kdcgarber/TRS-IO-SSD1306-M1/doc/rsc.png

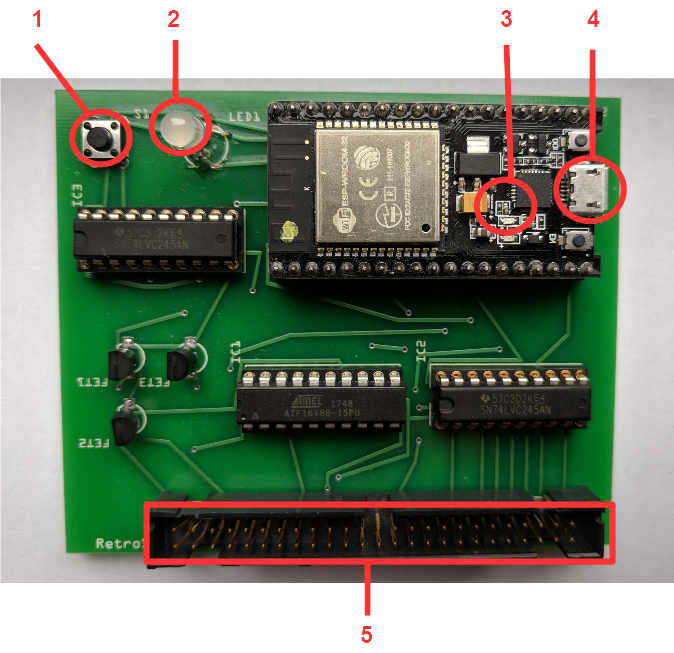
doc/rsc.png
