kdcgarber/TRS-IO-SSD1306-M1/doc/rsclient-1.png

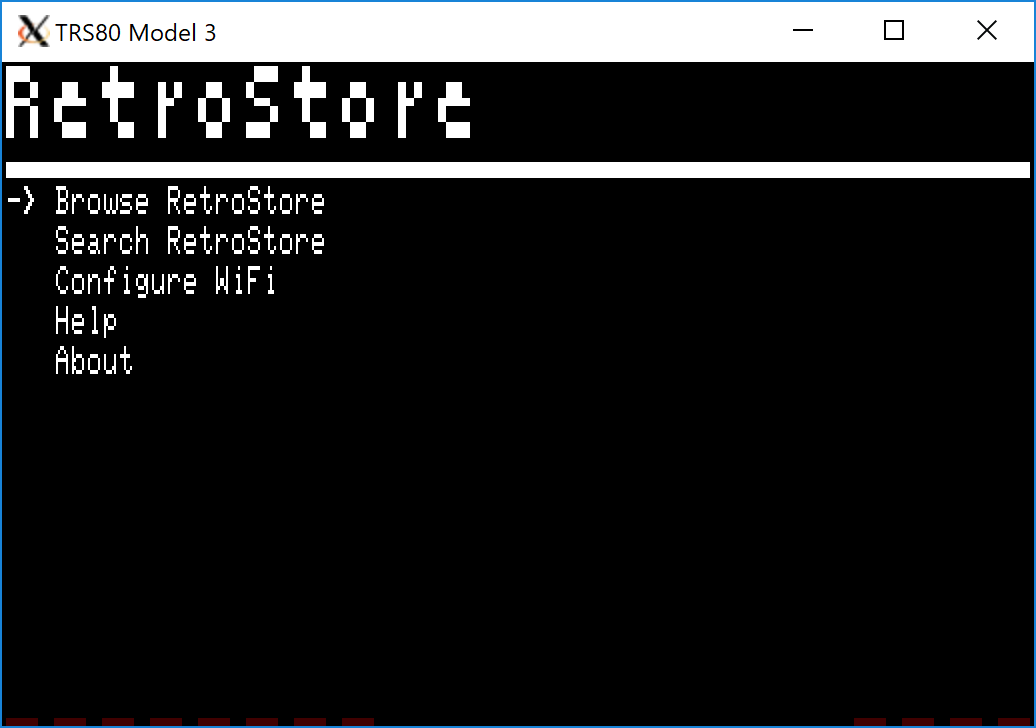
doc/rsclient-1.png
