kdcgarber/TRS-IO-SSD1306-M1/doc/trs-io-architecture.png

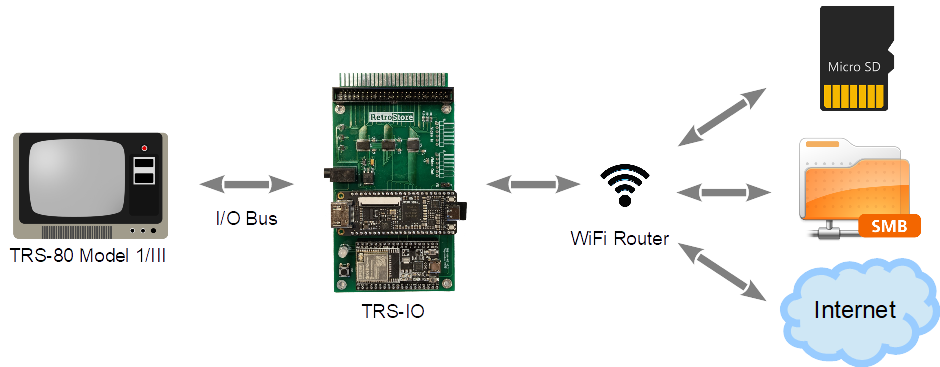
doc/trs-io-architecture.png
