kdcgarber/TRS-IO-SSD1306-M1/doc/trs-io-card-v1-labels.png

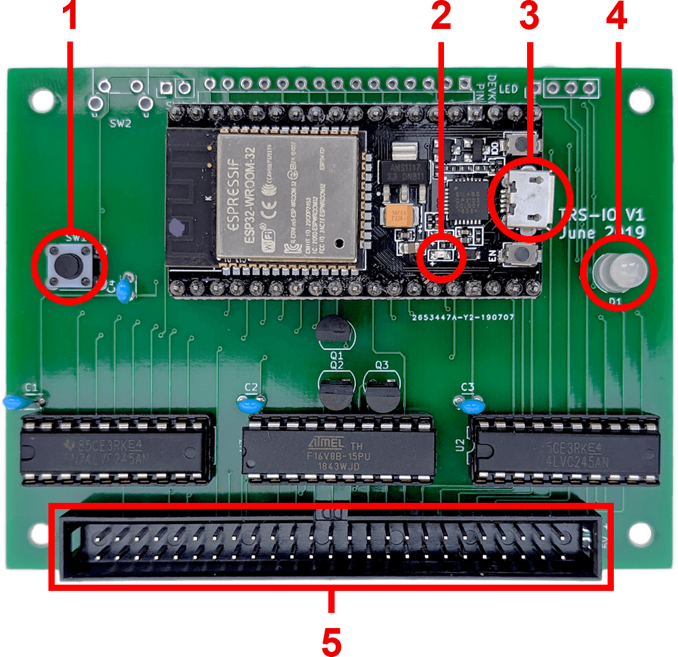
doc/trs-io-card-v1-labels.png
