kdcgarber/TRS-IO-SSD1306-M1/doc/trs-io-card-v1.png

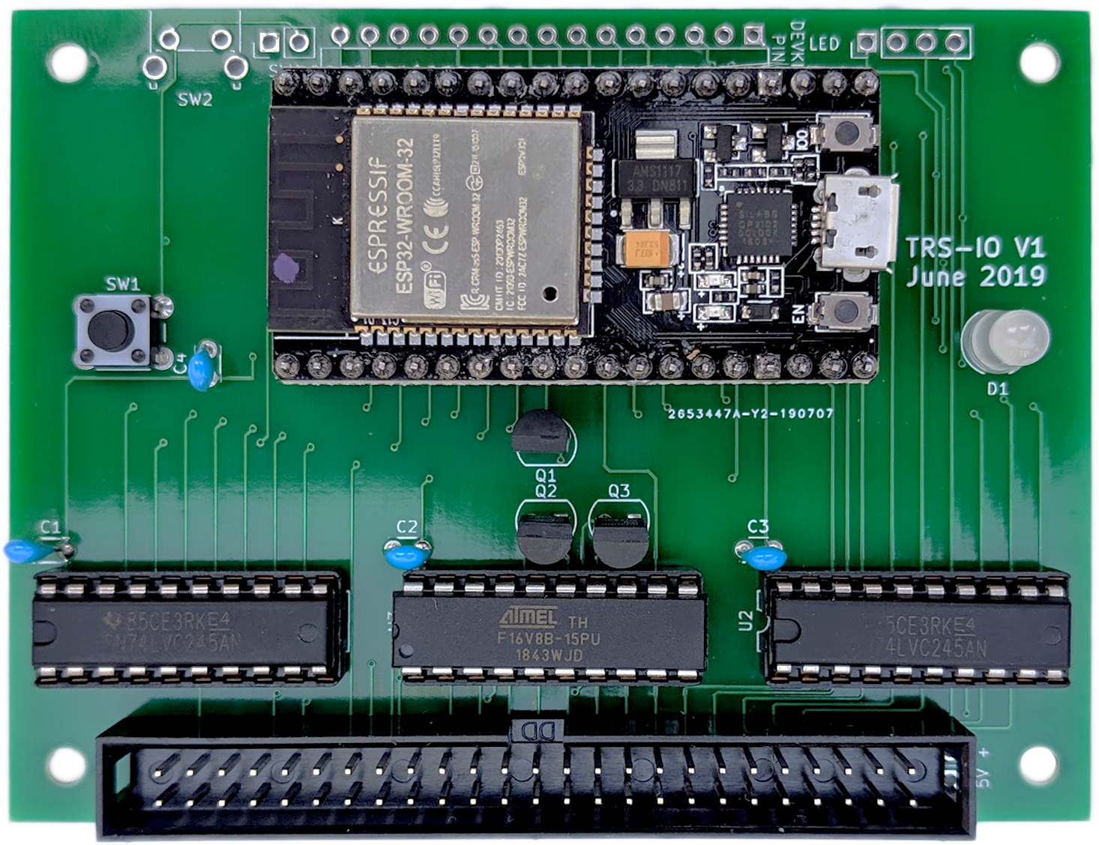
doc/trs-io-card-v1.png
