kdcgarber/TRS-IO-SSD1306-M1/doc/TRS-IO-M1-labels.png

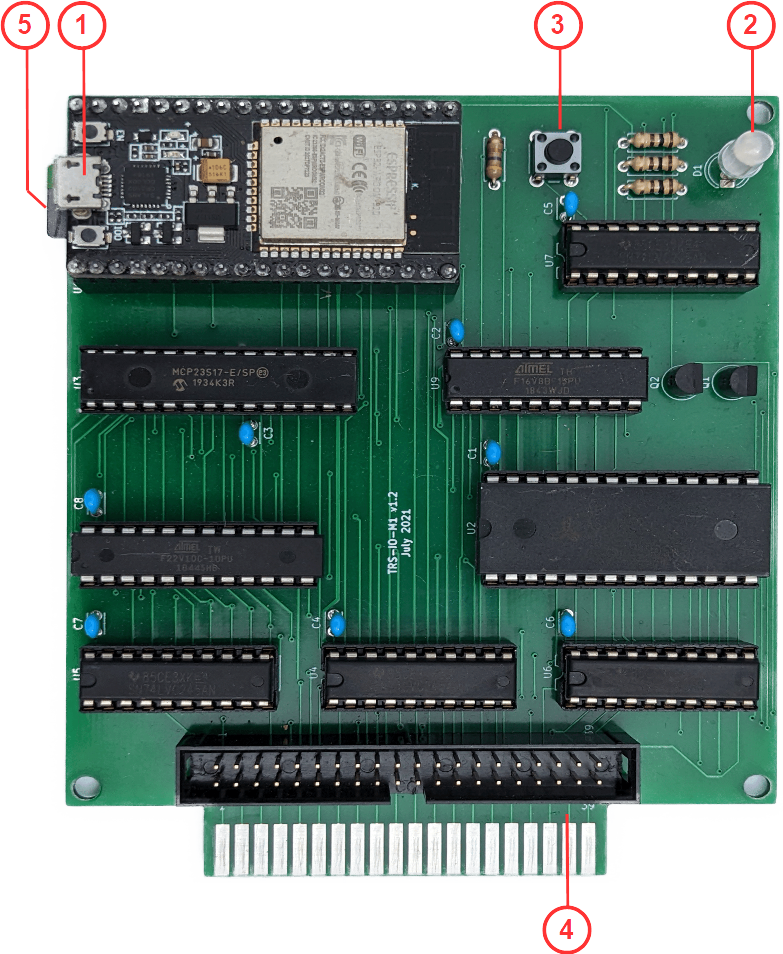
doc/TRS-IO-M1-labels.png
