kdcgarber/TRS-IO-SSD1306-M1/doc/TRS-IO-M1.png

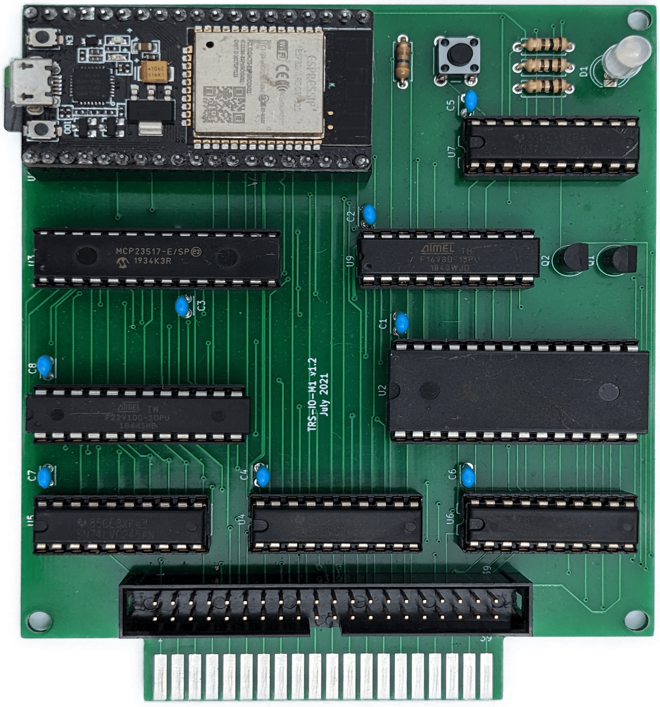
doc/TRS-IO-M1.png
