kdcgarber/TRS-IO-SSD1306-M1/doc/TRS-IO-M3-v2_2-labels.png

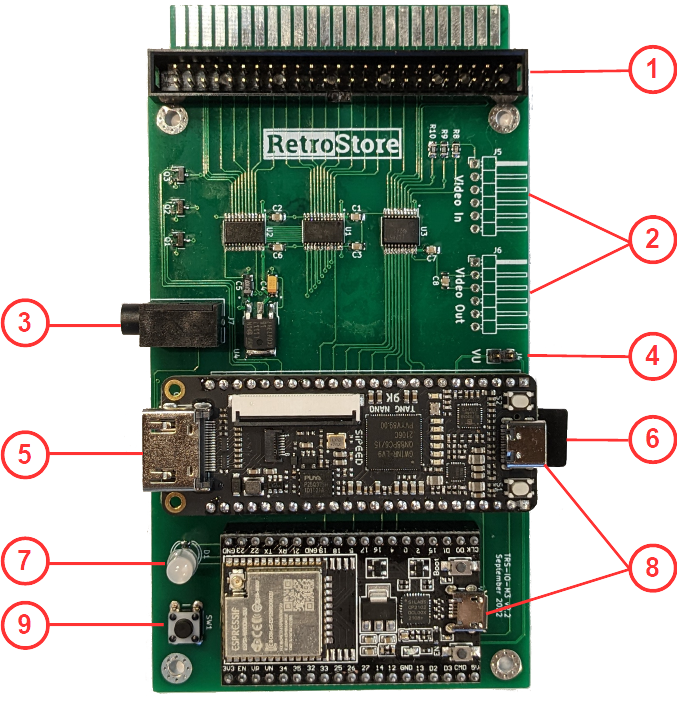
doc/TRS-IO-M3-v2_2-labels.png
