kdcgarber/TRS-IO-SSD1306-M1/doc/TRS-IO-M3-v2_2.png

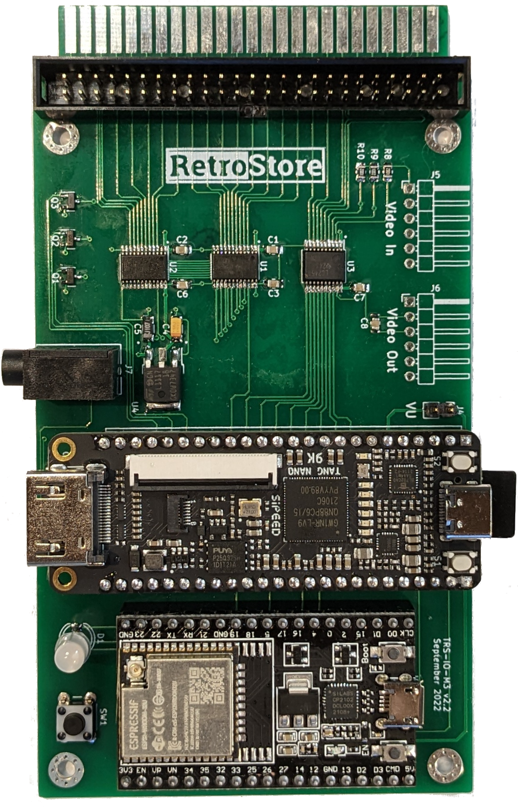
doc/TRS-IO-M3-v2_2.png
