kdcgarber/TRS-IO-SSD1306-M1/doc/TRS-IO-MIII-labels.png

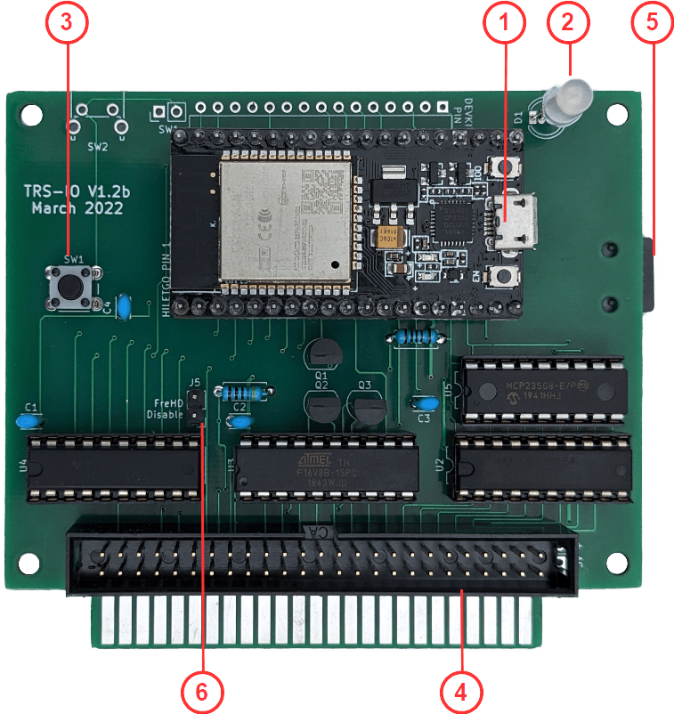
doc/TRS-IO-MIII-labels.png
