kdcgarber/TRS-IO-SSD1306-M1/doc/TRS-IO-MIII.png

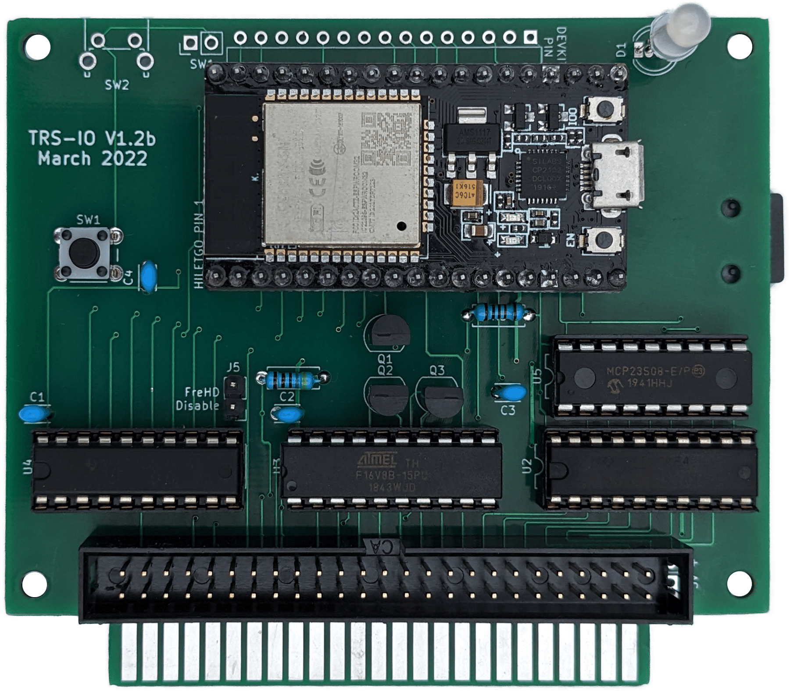
doc/TRS-IO-MIII.png
