kdcgarber/TRS-IO-SSD1306-M1/doc/TRS-IO-PP-v1_1-labels.png

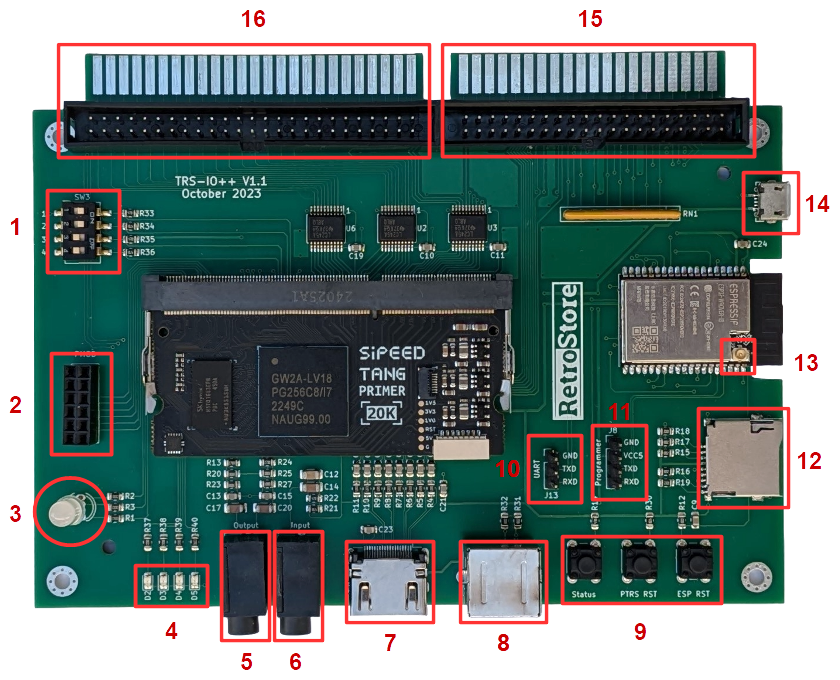
doc/TRS-IO-PP-v1_1-labels.png
