kdcgarber/TRS-IO-SSD1306-M1/doc/trs-io-web-ui.png

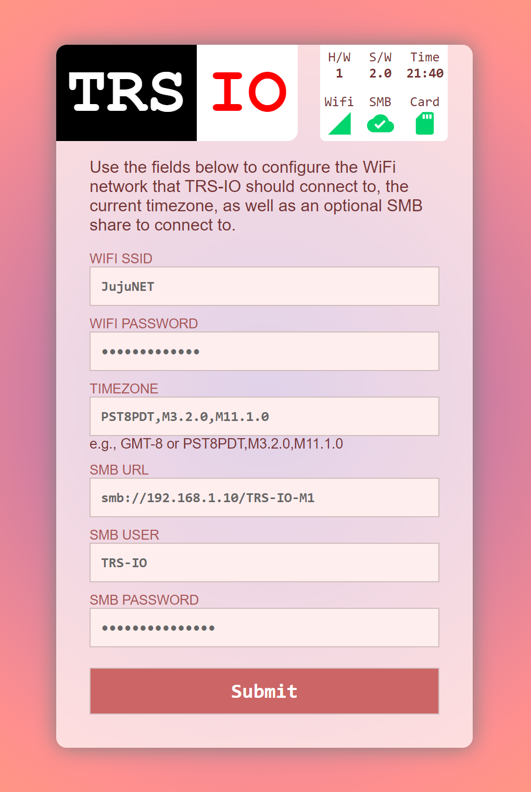
doc/trs-io-web-ui.png
