kdcgarber/TRS-IO-SSD1306-M1/images/BoardOnly2.jpg

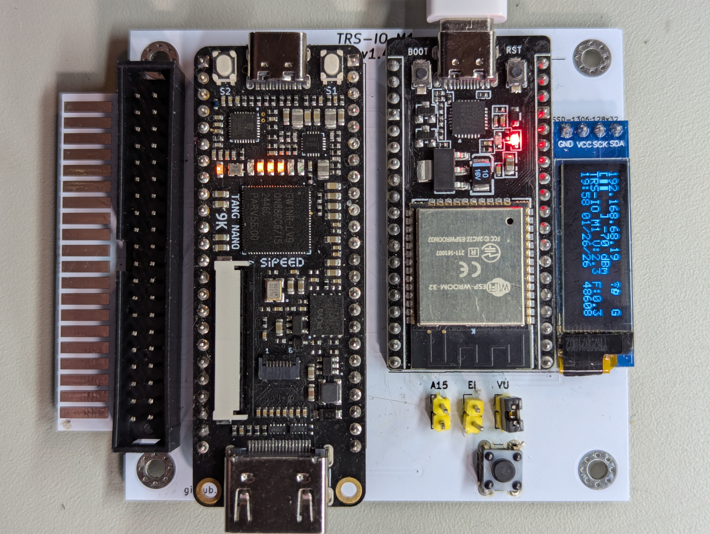
images/BoardOnly2.jpg
