kdcgarber/TRS-IO-SSD1306-M1/images/BoardOnly.jpg

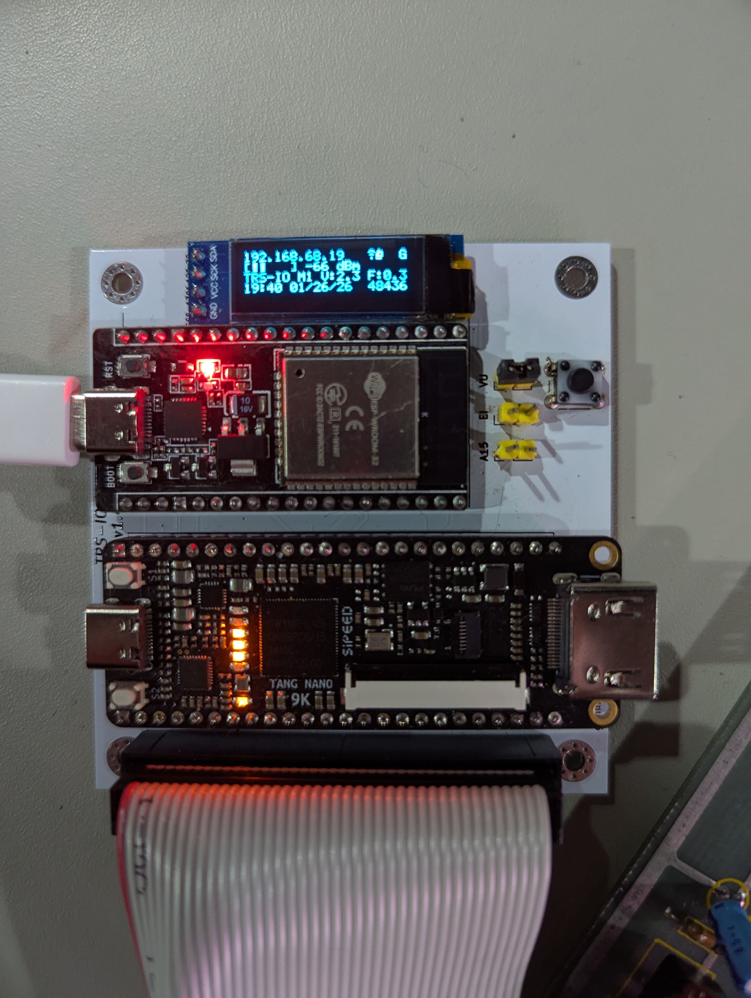
images/BoardOnly.jpg
