kdcgarber/TRS-IO-SSD1306-M1/images/InCase.jpg

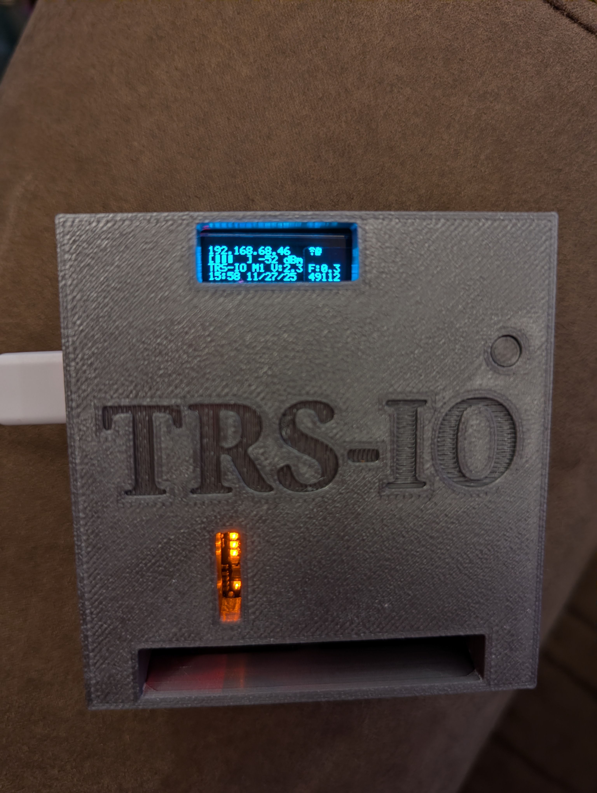
images/InCase.jpg
