kdcgarber/TRS-IO-SSD1306-M1/images/InCaseWithCable.jpg

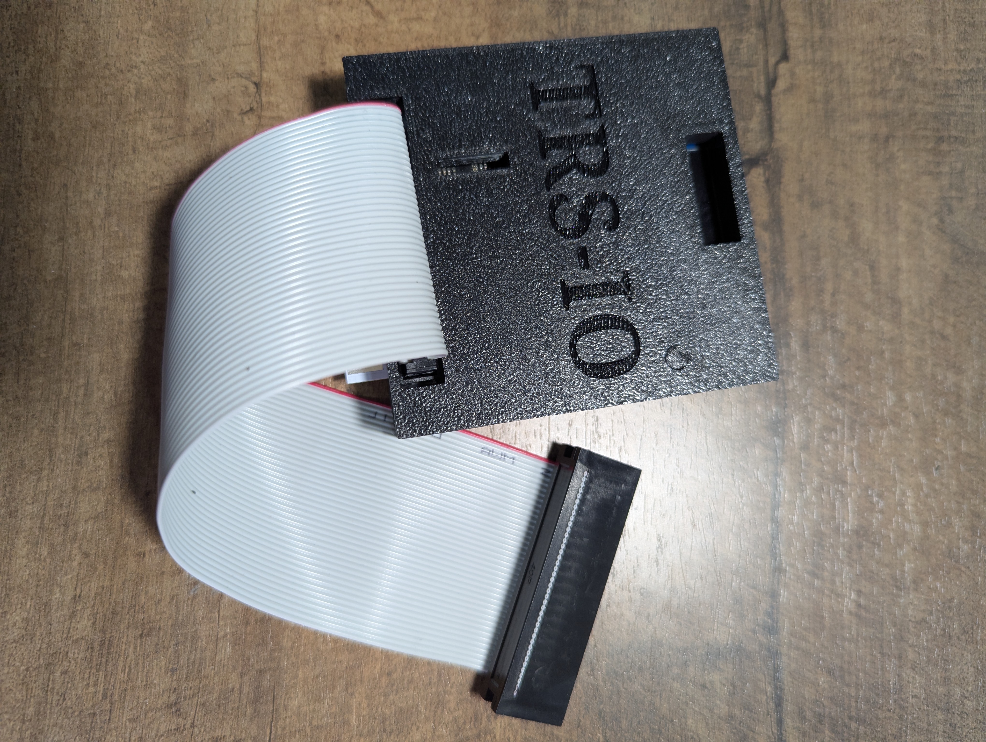
images/InCaseWithCable.jpg
