kdcgarber/TRS-IO-SSD1306-M1/images/PXL_20260127_015840978.PORTRAIT.ORIGINAL.jpg

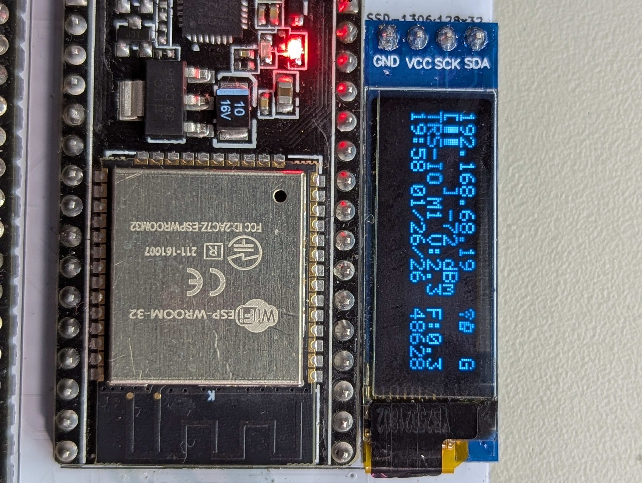
images/PXL_20260127_015840978.PORTRAIT.ORIGINAL.jpg
