kdcgarber/TRS-IO-SSD1306-M1/images/Side.jpg

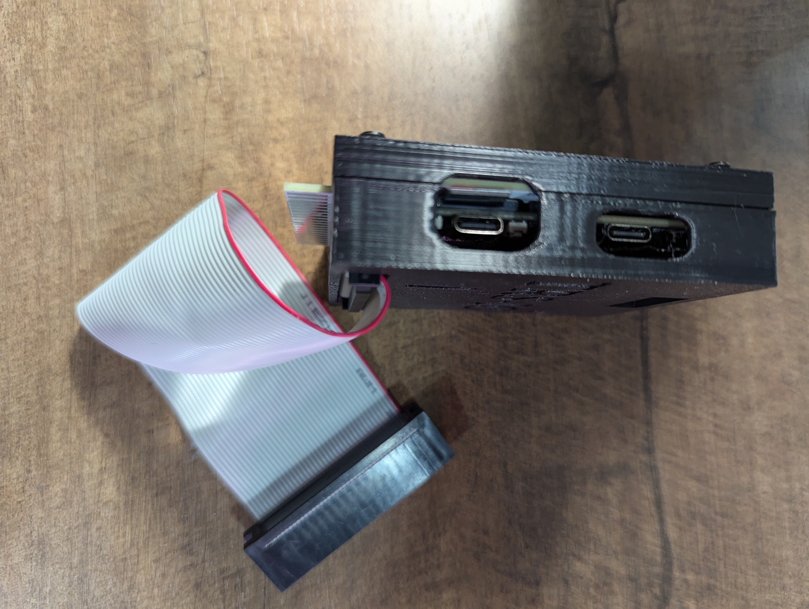
images/Side.jpg
