kdcgarber/TRS-IO-SSD1306-M1/images/SSD1306LCD.jpg

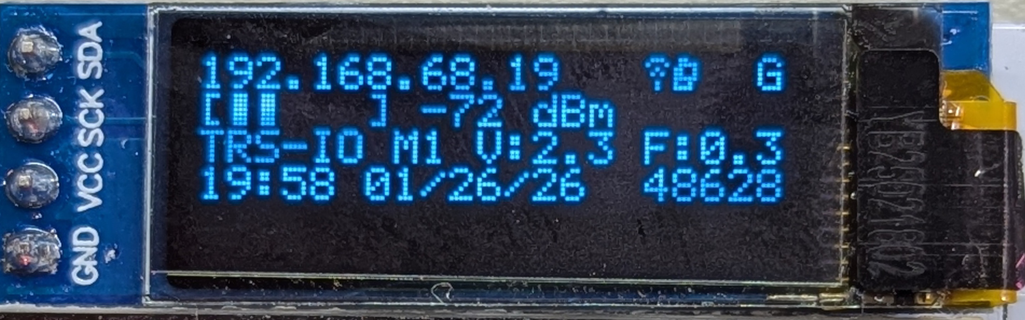
images/SSD1306LCD.jpg
