kdcgarber/TRS-IO-SSD1306-M1/src/images/help-guy.png

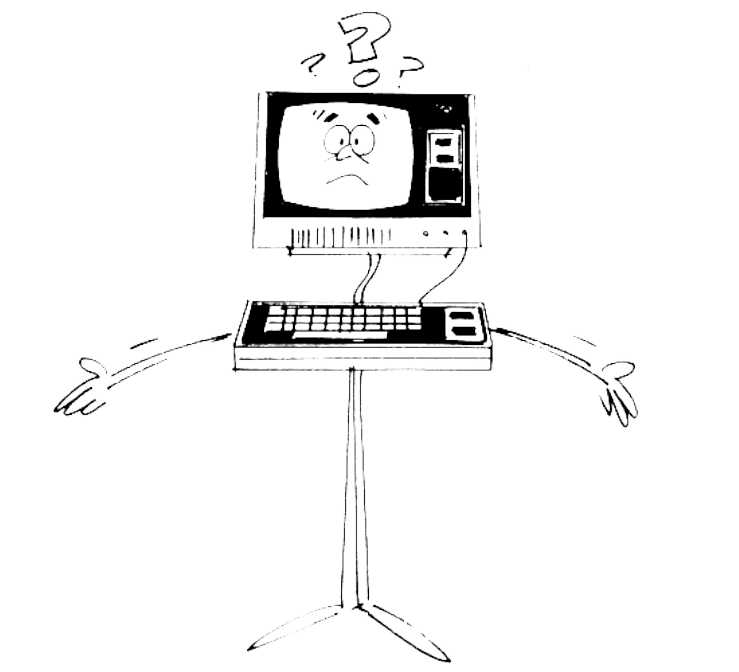
src/images/help-guy.png
