kdcgarber/TRS-IO-SSD1306-M1/src/trs/TRS-LIB/var/cap.gif

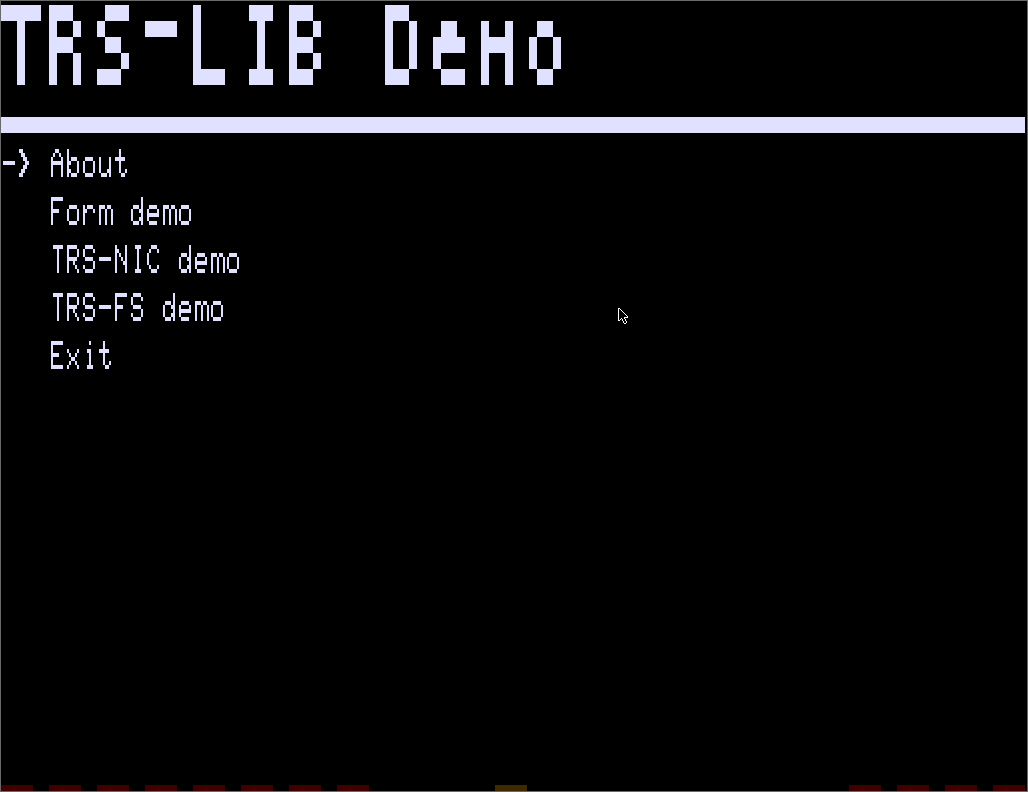
src/trs/TRS-LIB/var/cap.gif
