kdcgarber/TRS-IO-SSD1306-M1/src/esp/components/FabGL/examples/VGA/ClassicRacer/fotos.jpg

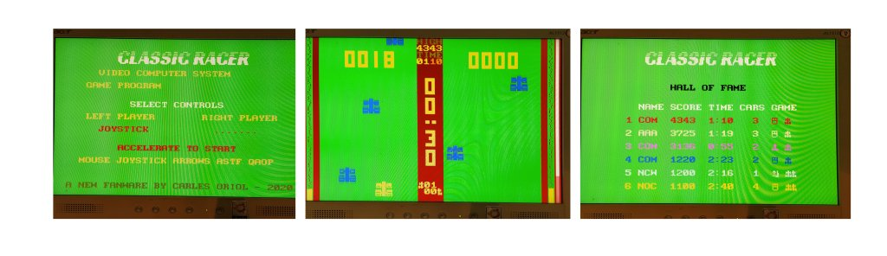
src/esp/components/FabGL/examples/VGA/ClassicRacer/fotos.jpg
