kdcgarber/TRS-IO-SSD1306-M1/src/esp/components/FabGL/images/github.png

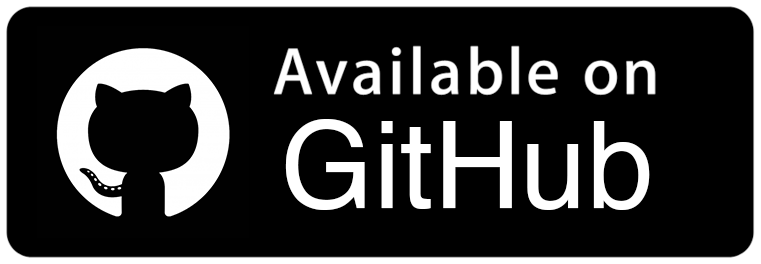
src/esp/components/FabGL/images/github.png
