kdcgarber/TRS-IO-SSD1306-M1/src/esp/components/FabGL/images/schema_audio.png

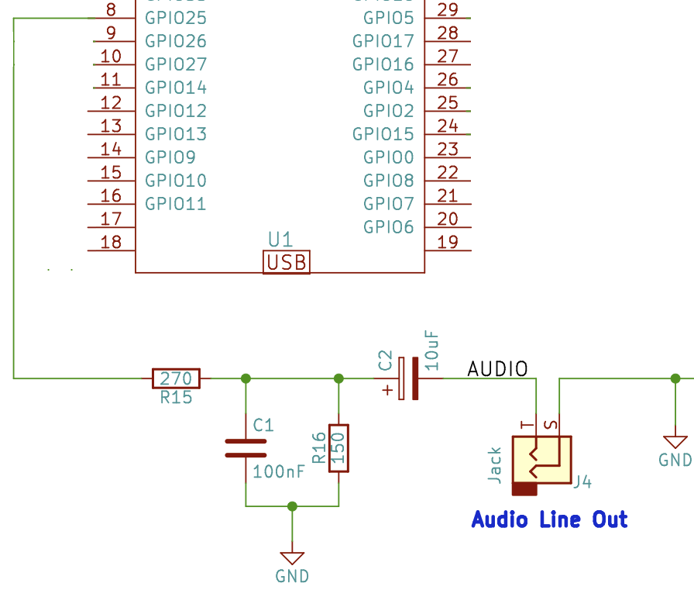
src/esp/components/FabGL/images/schema_audio.png
