kdcgarber/TRS-IO-SSD1306-M1/doc/rs_bodge_fix.jpg

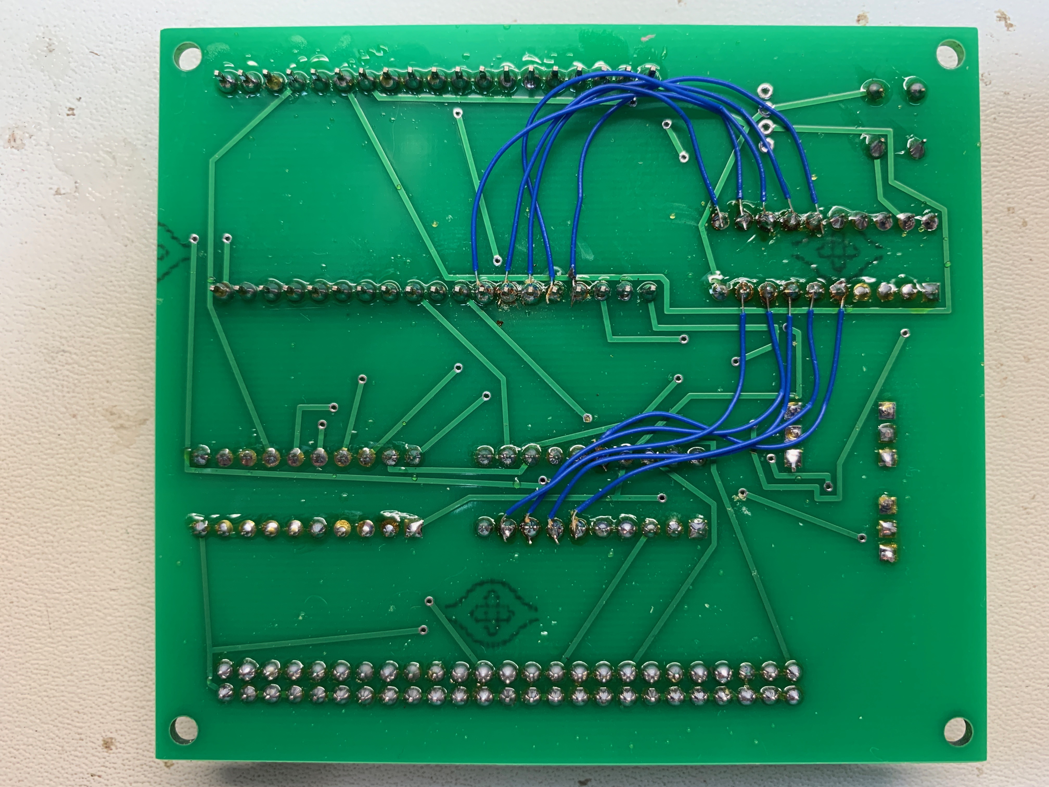
doc/rs_bodge_fix.jpg
