kdcgarber/TRS-IO-SSD1306-M1/images/BuildAndInCasejpg.jpg

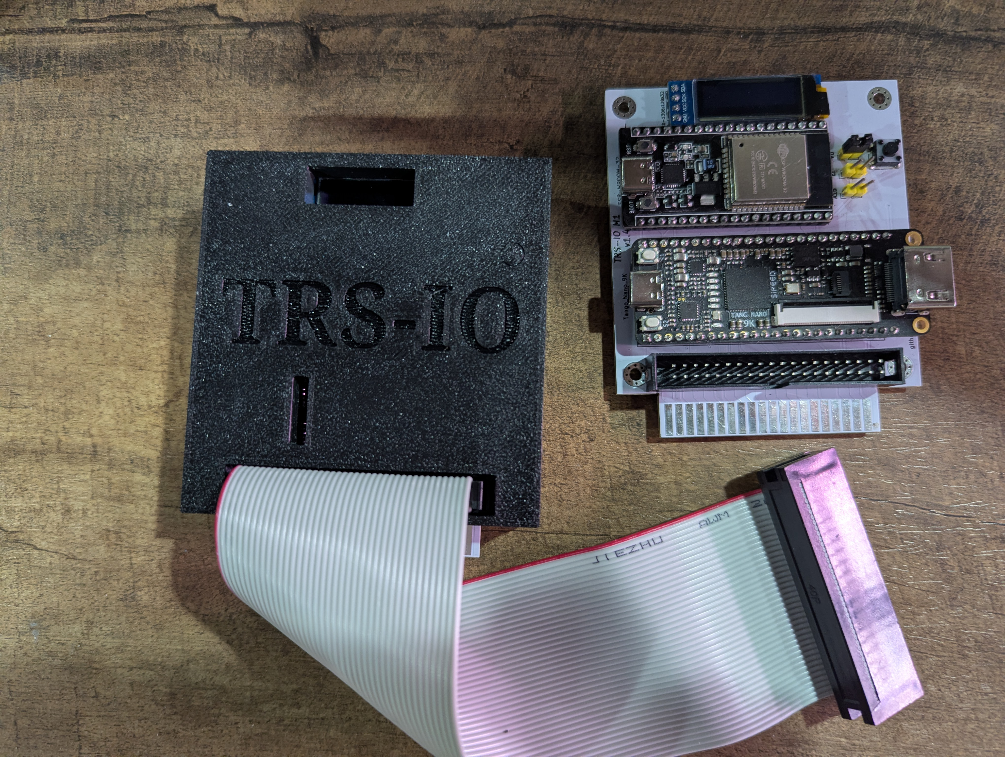
images/BuildAndInCasejpg.jpg
